makinteract/MagnID/Software/AndroidApps/BRIDGEapp3/data/bg.png

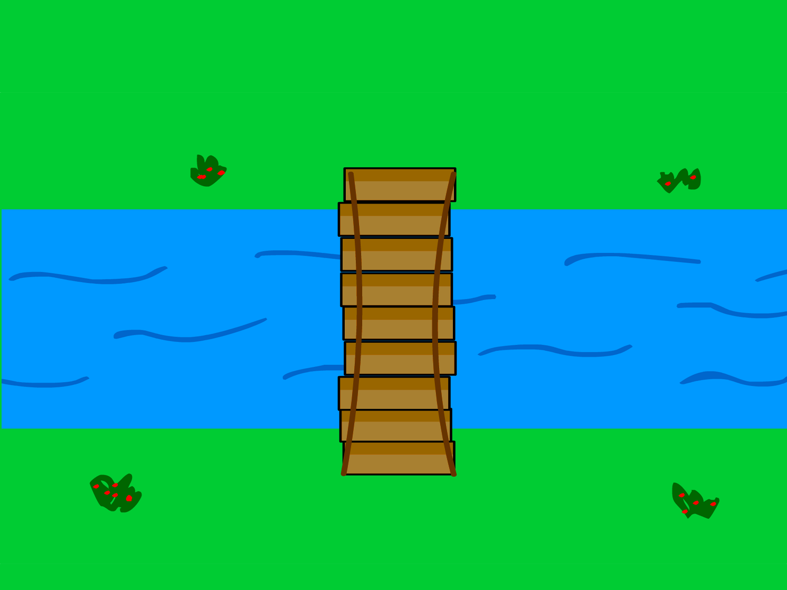
Software/AndroidApps/BRIDGEapp3/data/bg.png
