makinteract/MagnID/Software/AndroidApps/BRIDGEapp3/data/chicken.png

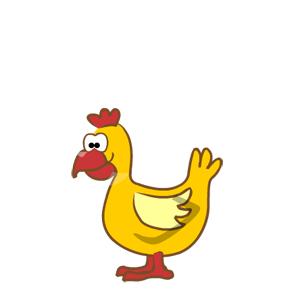
Software/AndroidApps/BRIDGEapp3/data/chicken.png
