makinteract/MagnID/Software/AndroidApps/BRIDGEapp3/data/farmer.png

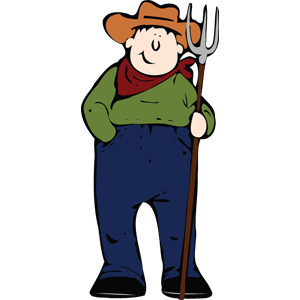
Software/AndroidApps/BRIDGEapp3/data/farmer.png
