makinteract/MagnID/Software/AndroidApps/BRIDGEapp3/data/fox.png

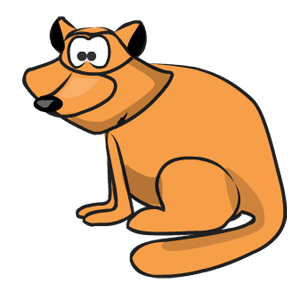
Software/AndroidApps/BRIDGEapp3/data/fox.png
