makinteract/MagnID/Software/AndroidApps/BRIDGEapp3/data/wheat.png

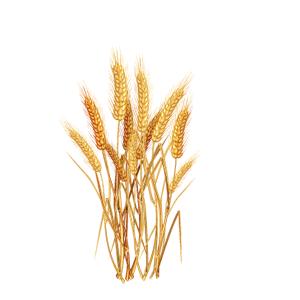
Software/AndroidApps/BRIDGEapp3/data/wheat.png
