makinteract/MagnID/Software/AndroidApps/FLAGSapp/data/bg.png

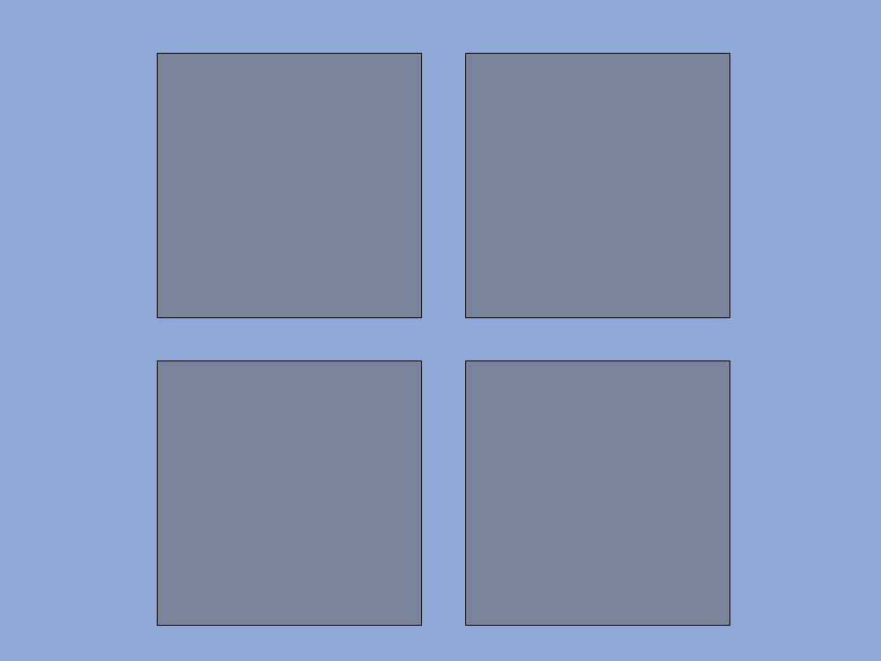
Software/AndroidApps/FLAGSapp/data/bg.png
