makinteract/MagnID/Software/AndroidApps/FLAGSapp/data/flags/english.png

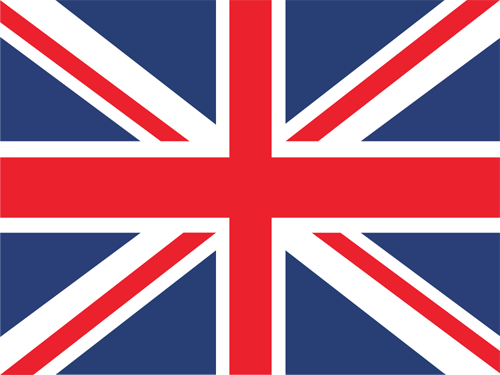
Software/AndroidApps/FLAGSapp/data/flags/english.png
