makinteract/MagnID/Software/AndroidApps/FLAGSapp/data/flags/french.png

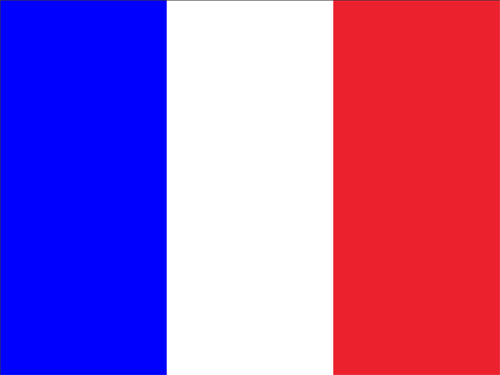
Software/AndroidApps/FLAGSapp/data/flags/french.png
