makinteract/MagnID/Software/AndroidApps/FLAGSapp/data/flags/german.png

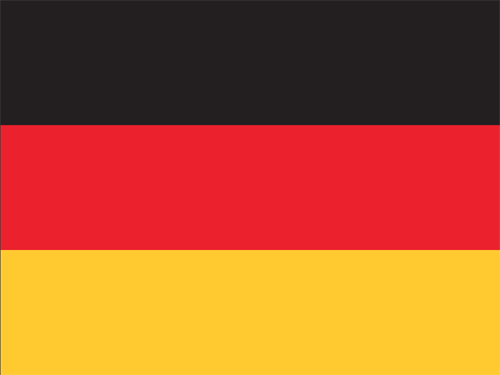
Software/AndroidApps/FLAGSapp/data/flags/german.png
