makinteract/MagnID/Software/AndroidApps/FLAGSapp/data/flags/portuguese.png

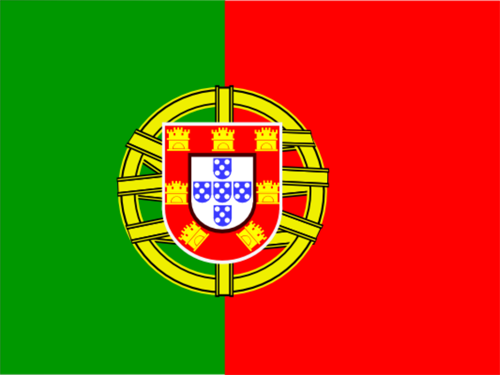
Software/AndroidApps/FLAGSapp/data/flags/portuguese.png
