makinteract/MagnID/Software/AndroidApps/FLAGSapp/data/flags/spanish.png

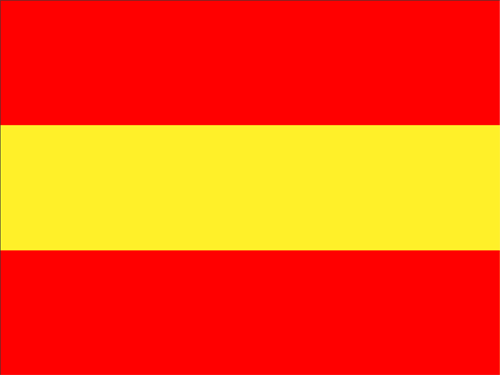
Software/AndroidApps/FLAGSapp/data/flags/spanish.png
