makinteract/MagnID/Software/AndroidApps/FLAGSapp/data/src/languages.band/Output/arrange_screenshot.tiff

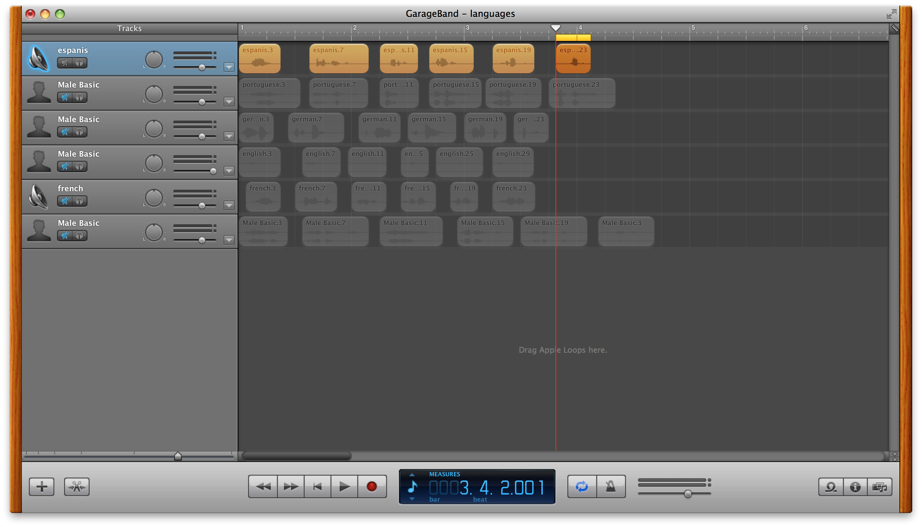
Software/AndroidApps/FLAGSapp/data/src/languages.band/Output/arrange_screenshot.tiff
