makinteract/MagnID/Software/AndroidApps/IDapp/data/imgs/all.png

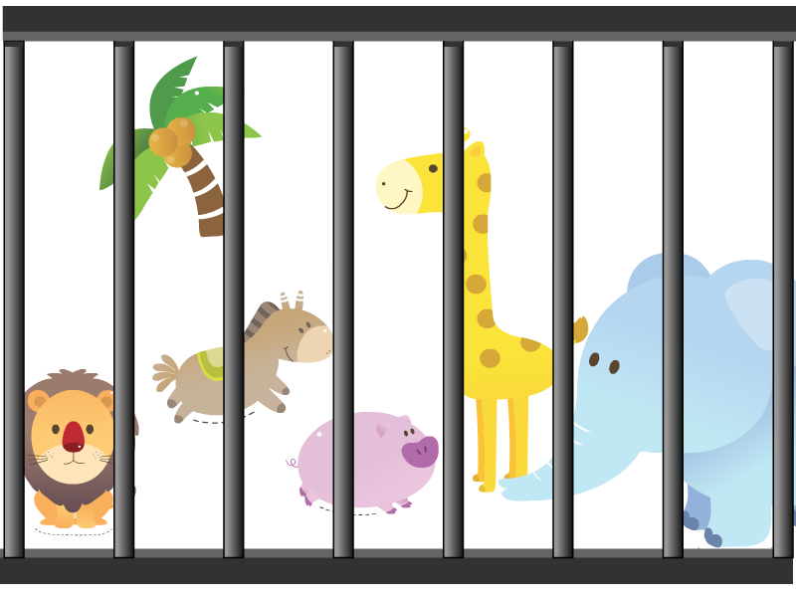
Software/AndroidApps/IDapp/data/imgs/all.png
