makinteract/MagnID/Software/AndroidApps/IDapp/data/imgs/bg.png

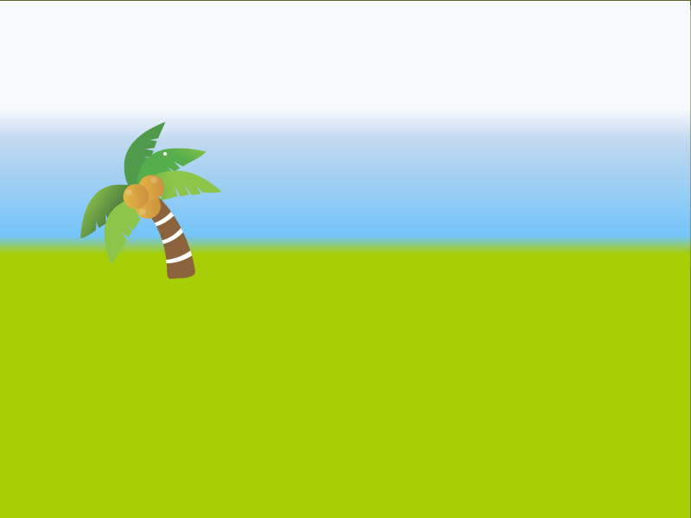
Software/AndroidApps/IDapp/data/imgs/bg.png
