makinteract/MagnID/Software/AndroidApps/IDapp/data/imgs/elephant.png

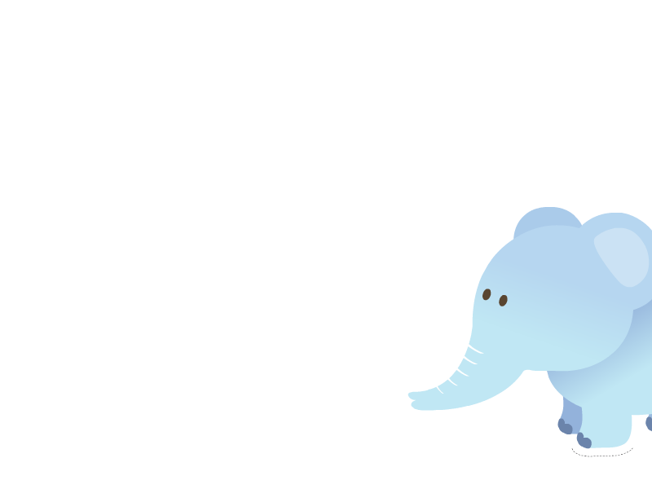
Software/AndroidApps/IDapp/data/imgs/elephant.png
