makinteract/MagnID/Software/AndroidApps/IDapp/data/imgs/empty.png

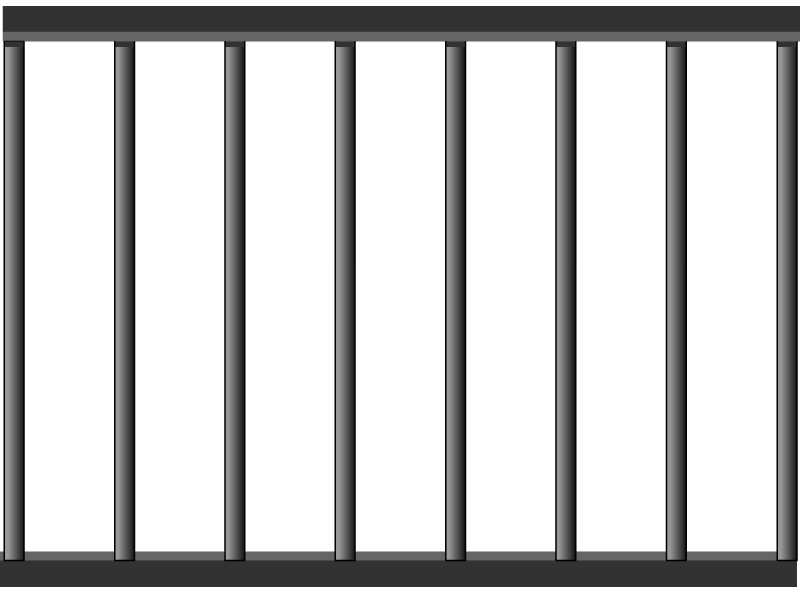
Software/AndroidApps/IDapp/data/imgs/empty.png
