makinteract/MagnID/Software/AndroidApps/IDapp/data/imgs/giraffe.png

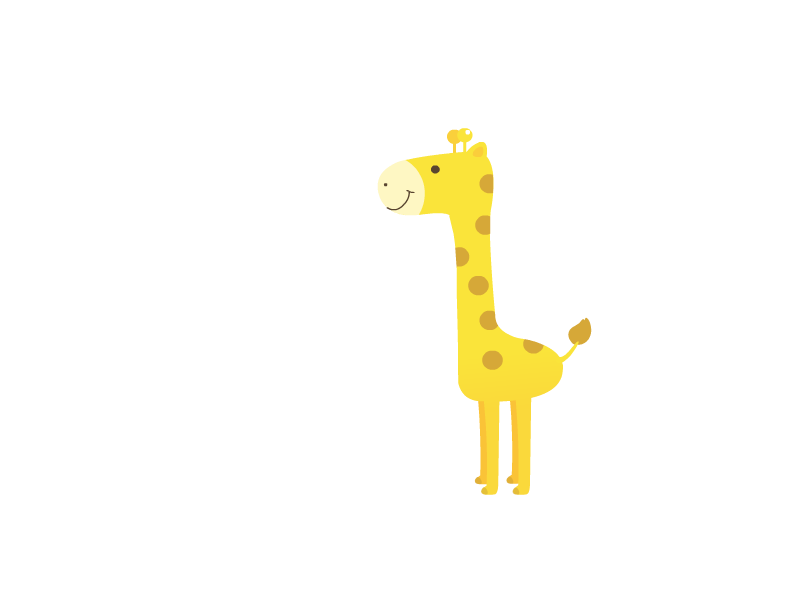
Software/AndroidApps/IDapp/data/imgs/giraffe.png
