makinteract/MagnID/Software/AndroidApps/IDapp/data/imgs/horse.png

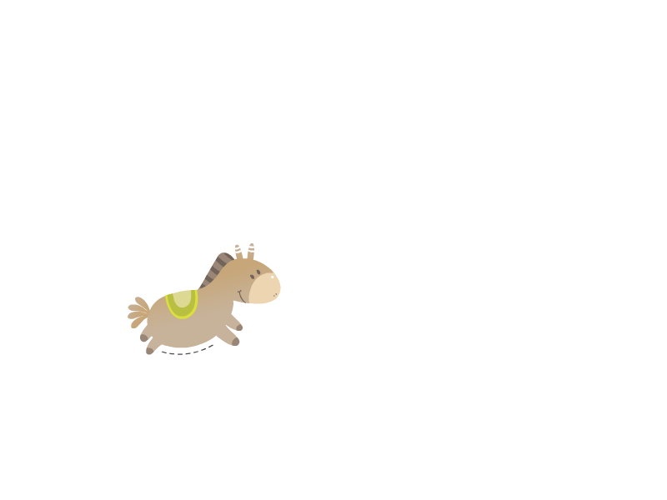
Software/AndroidApps/IDapp/data/imgs/horse.png
