makinteract/MagnID/Software/AndroidApps/IDapp/data/imgs/lion.png

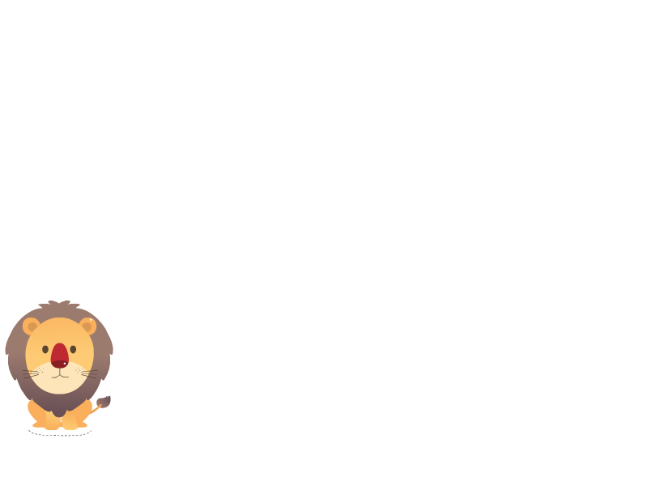
Software/AndroidApps/IDapp/data/imgs/lion.png
