makinteract/MagnID/Software/AndroidApps/IDapp/data/imgs/pig.png

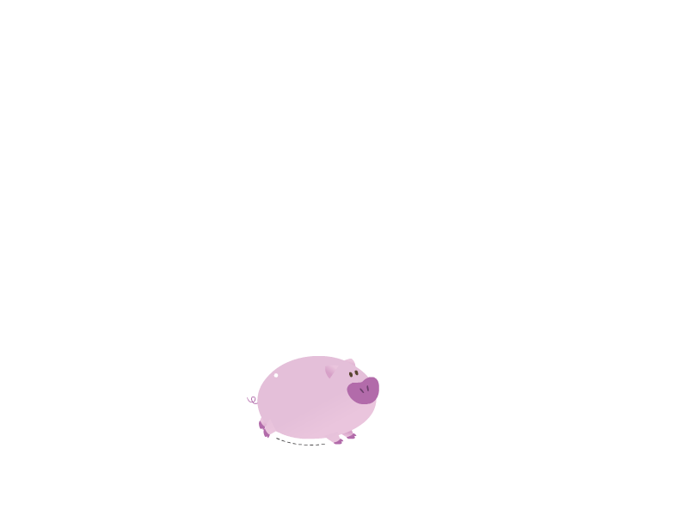
Software/AndroidApps/IDapp/data/imgs/pig.png
