makinteract/MagnID/Software/AndroidApps/IDapp/data/toPrint/cage.jpg

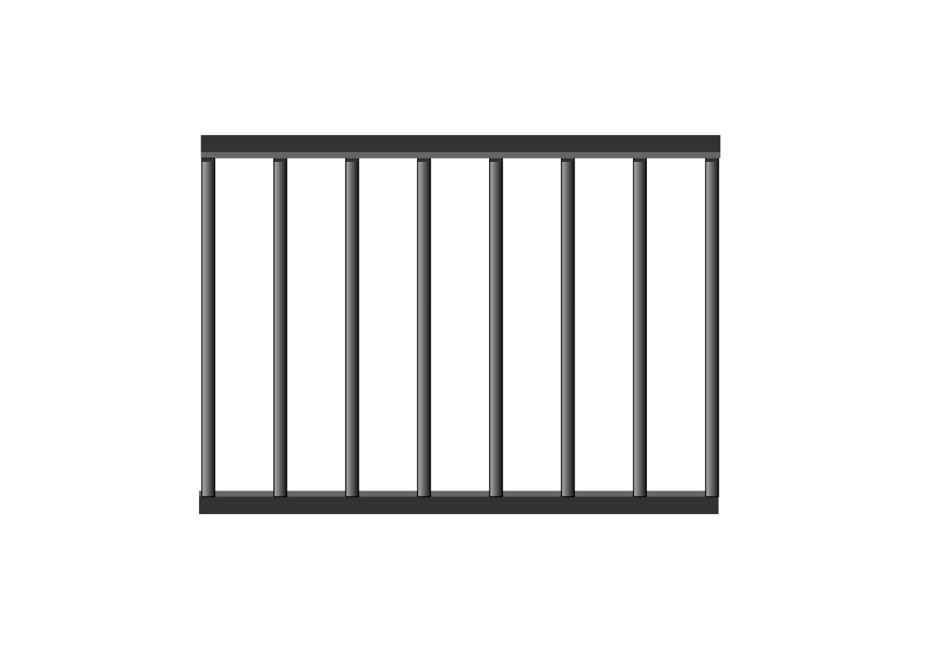
Software/AndroidApps/IDapp/data/toPrint/cage.jpg
